MisterHW/FX10AMCUCT/MCU-FX10-template.sch

## KiCad design MCU-FX10-template.sch (2020-05-31)

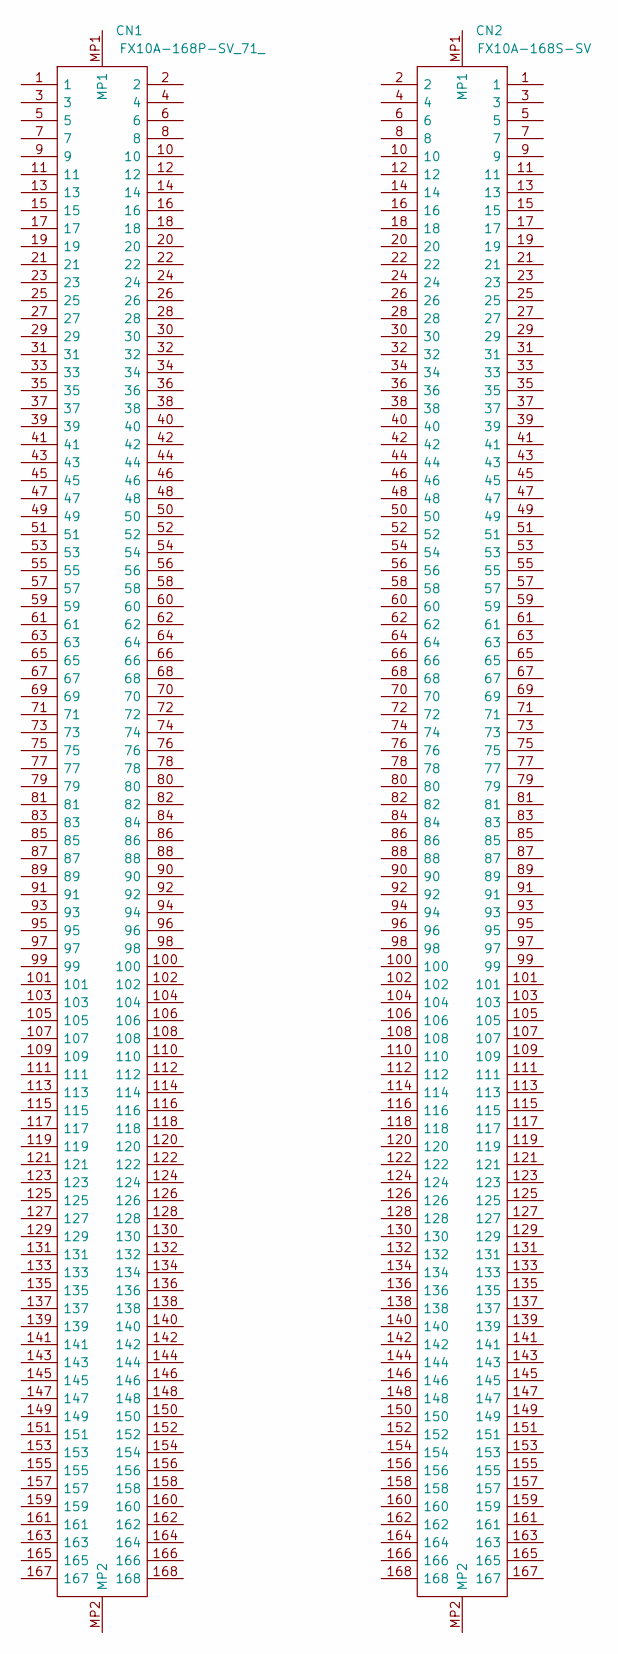
[picture p7: schematic MCU-FX10-template.sch]

Parts:
CN1: FX10A-168P-SV_71_; Manufacturer_Part_Number FX10A-168P-SV(71); Mouser Part Number 798-FX10A168PSV71
CN2: FX10A-168S-SV; Manufacturer_Part_Number FX10A-168S-SV; Mouser Part Number 798-FX10A168SSV
